YodaheWondimu/Stardeck/assets/architecture/System-Architecture-A3.png

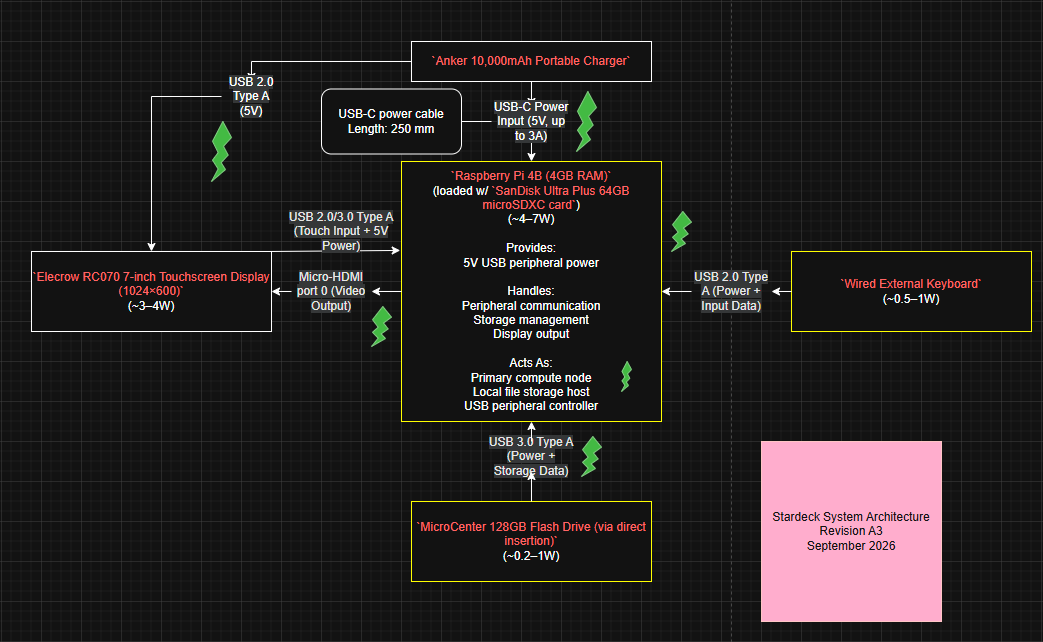
assets/architecture/System-Architecture-A3.png
