YodaheWondimu/Stardeck/assets/designs/Internal-View.png

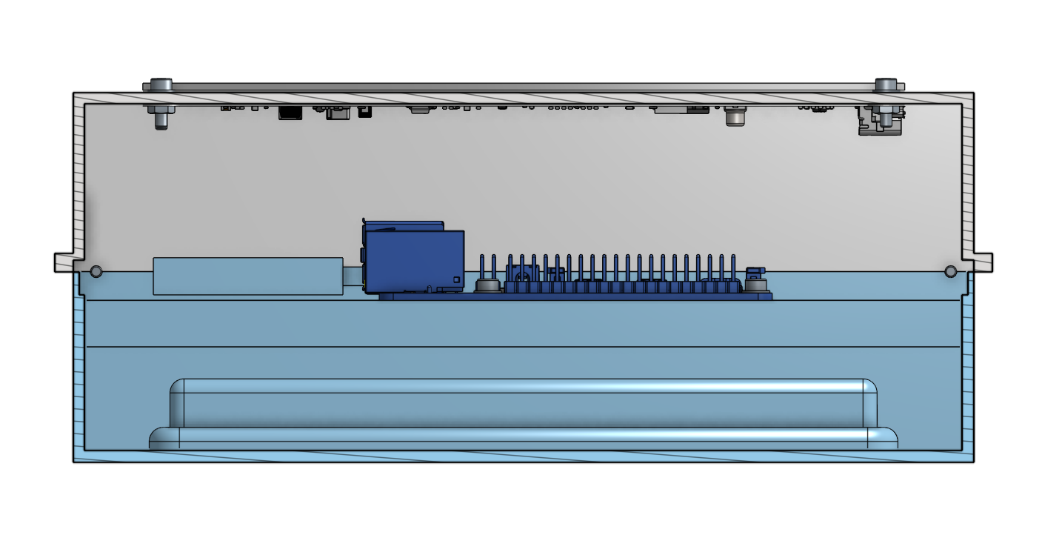
assets/designs/Internal-View.png
