YodaheWondimu/Stardeck/assets/designs/Pi-Mounting-View.png

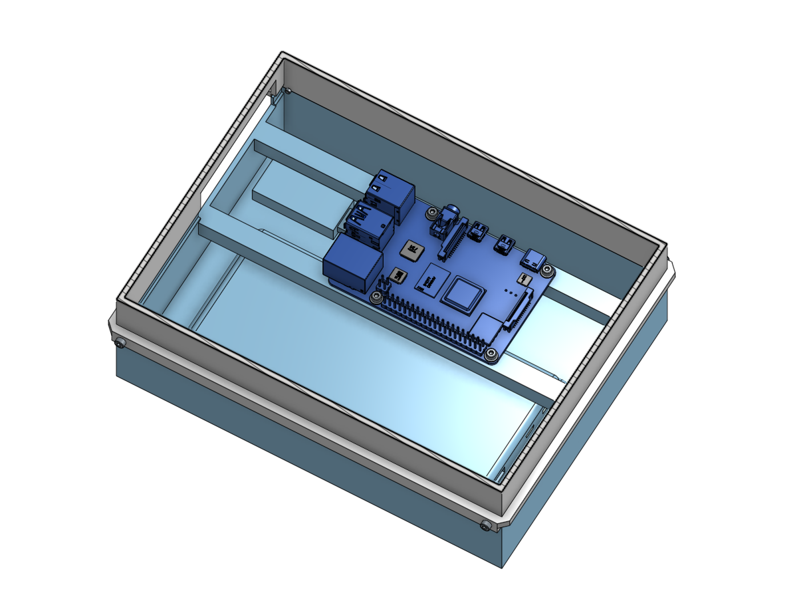
assets/designs/Pi-Mounting-View.png
