YodaheWondimu/Stardeck/assets/designs/Revised-Isometric-View.png

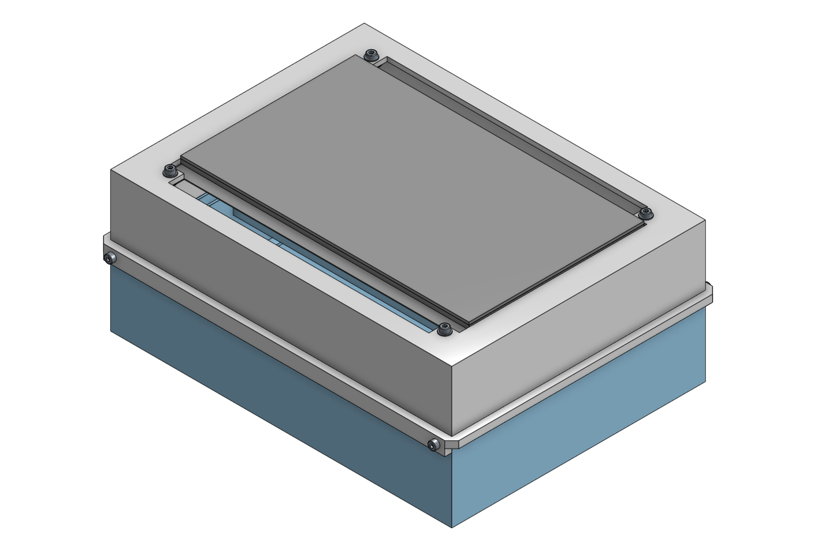
assets/designs/Revised-Isometric-View.png
