YodaheWondimu/Stardeck/assets/designs/Starter-Enclosure-Top.png

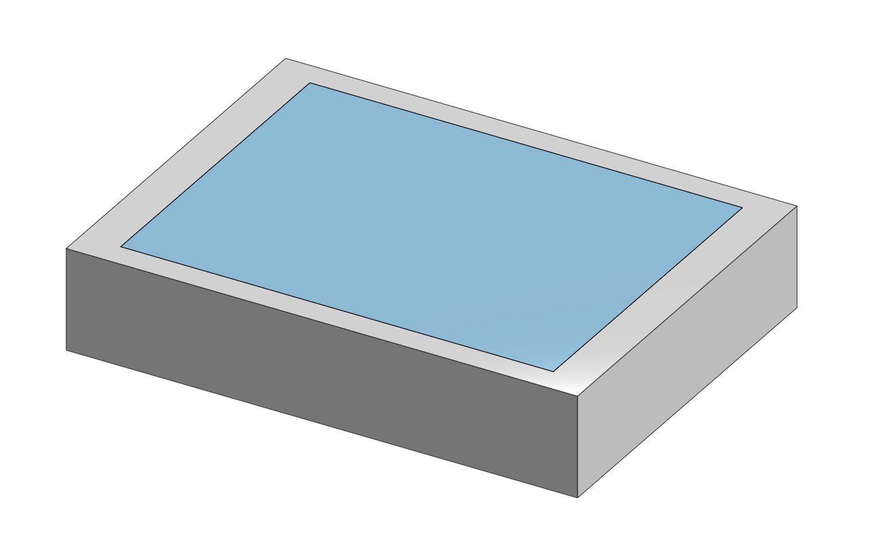
assets/designs/Starter-Enclosure-Top.png
